Xinyuan-LilyGO/T-Display-C5/examples/touch/touch.ino

/*
   MIT License

  Copyright (c) 2021 Felix Biego

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
  THE SOFTWARE IS PROVIDED "AS IS", WITHOUT WARRANTY OF ANY KIND, EXPRESS OR
  IMPLIED, INCLUDING BUT NOT LIMITED TO THE WARRANTIES OF MERCHANTABILITY,
  FITNESS FOR A PARTICULAR PURPOSE AND NONINFRINGEMENT. IN NO EVENT SHALL THE
  AUTHORS OR COPYRIGHT HOLDERS BE LIABLE FOR ANY CLAIM, DAMAGES OR OTHER
  LIABILITY, WHETHER IN AN ACTION OF CONTRACT, TORT OR OTHERWISE, ARISING FROM,
  OUT OF OR IN CONNECTION WITH THE SOFTWARE OR THE USE OR OTHER DEALINGS IN THE
  SOFTWARE.
*/

#include <CST816S.h>
#include "Arduino.h"
#include "board_config.h"


CST816S touch(IIC_SDA_PIN, IIC_SCL_PIN, -1, TP_INT); // sda, scl, rst, irq

volatile bool touchEventFlag = false;

// Interrupt function to set the flag
void IRAM_ATTR onTouchInterrupt()
{
    touchEventFlag = true;
}

void setup()
{
    Serial.begin(115200);
    Wire.begin(IIC_SDA_PIN, IIC_SCL_PIN);

    touch.begin(RISING);
    touch.attachUserInterrupt(onTouchInterrupt);
    // touch.enable_double_click(); // Enable double-click detection

    Serial.print(touch.data.version);
    Serial.print("\t");
    Serial.print(touch.data.versionInfo[0]);
    Serial.print("-");
    Serial.print(touch.data.versionInfo[1]);
    Serial.print("-");
    Serial.println(touch.data.versionInfo[2]);
}

void loop()
{
    if (touchEventFlag)
    {
        touchEventFlag = false; // Clear the flag
        if (touch.available())
        {
            Serial.print(touch.gesture());
            Serial.print("     \t");
            Serial.print(touch.data.points);
            Serial.print("\t");
            Serial.print(touch.data.event);
            Serial.print("\t");
            Serial.print(touch.data.x);
            Serial.print("\t");
            Serial.println(touch.data.y);
        }
    }
}
